mihirus/sm-thesis/cad/leakage-transformer-assembly/shunt-heat-sink.SLDPRT

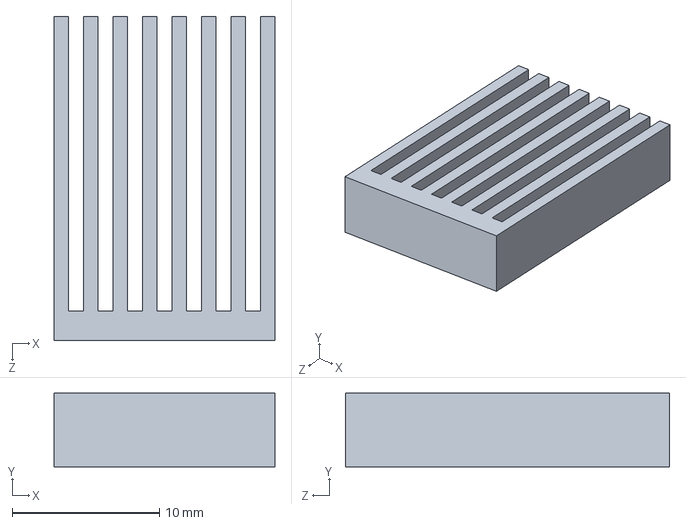
[picture p15: CAD file, 2025-12-01]
cad/leakage-transformer-assembly/shunt-heat-sink.SLDPRT
15.0 x 5.00 x 22.0 mm
