mihirus/sm-thesis/pcb/custom_assets/RM-0505S_P.step

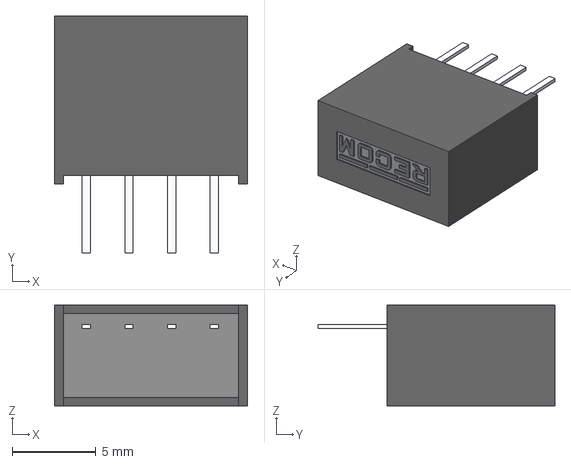
[picture p16: CAD file, 2025-12-01]
pcb/custom_assets/RM-0505S_P.step
11.5 x 14.1 x 6.00 mm
