mihirus/sm-thesis/cad/cores/etd59_core.SLDPRT

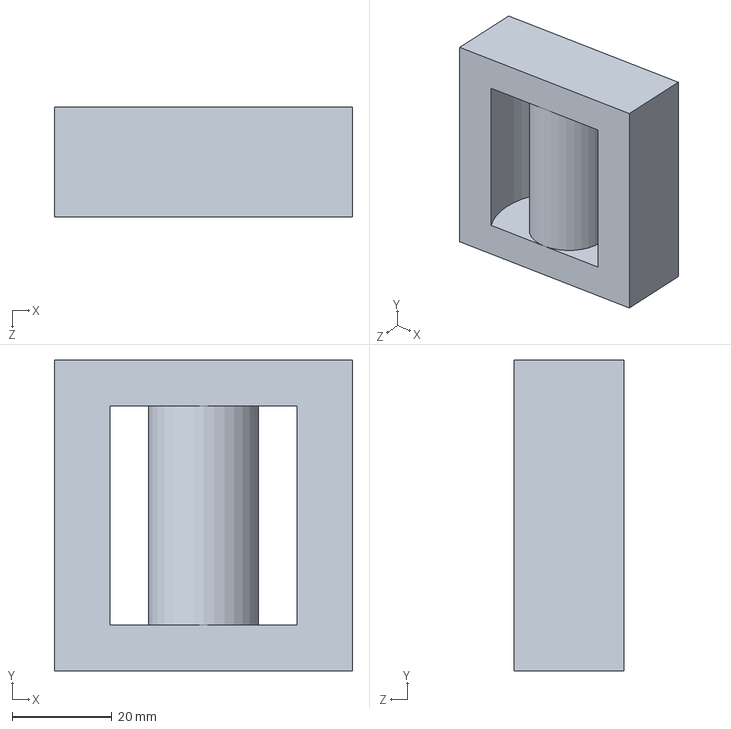
[picture p17: CAD file, 2025-12-01]
cad/cores/etd59_core.SLDPRT
59.8 x 62.4 x 22.1 mm
