mihirus/sm-thesis/cad/leakage-transformer-assembly/ETD59-integrated-base-raised-nov21.SLDPRT

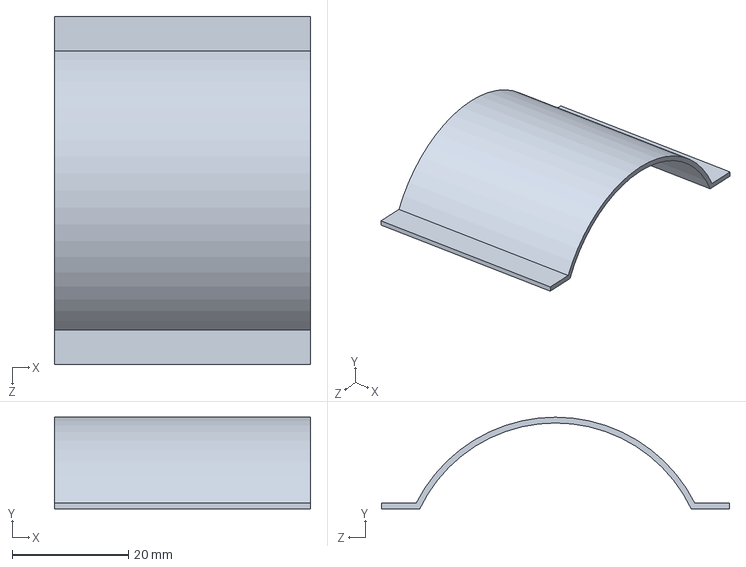
[picture p18: CAD file, 2025-12-01]
cad/leakage-transformer-assembly/ETD59-integrated-base-raised-nov21.SLDPRT
44.0 x 15.8 x 59.8 mm
