mihirus/sm-thesis/cad/leakage-transformer-assembly/ETD59-integrated-top-raised-0.8mm-dec9.SLDPRT

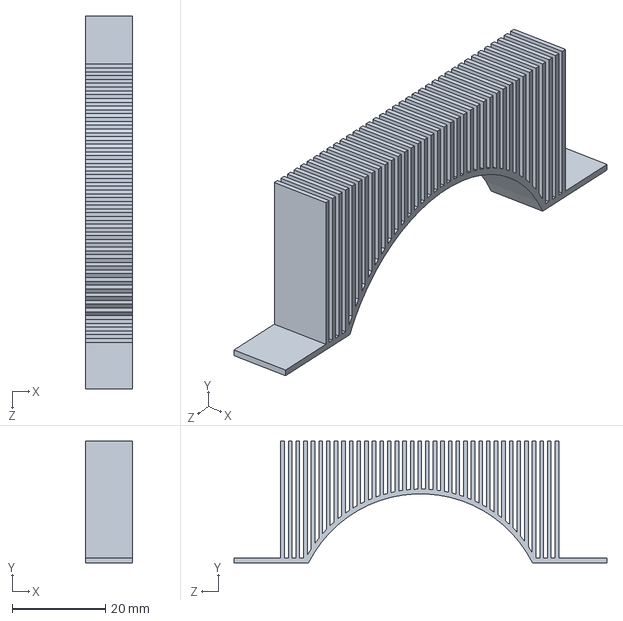
[picture p19: CAD file, 2025-12-01]
cad/leakage-transformer-assembly/ETD59-integrated-top-raised-0.8mm-dec9.SLDPRT
10.0 x 26.0 x 79.8 mm
