mihirus/sm-thesis/cad/leakage-transformer-assembly/etd59_bobbin_integrated_v7.SLDPRT

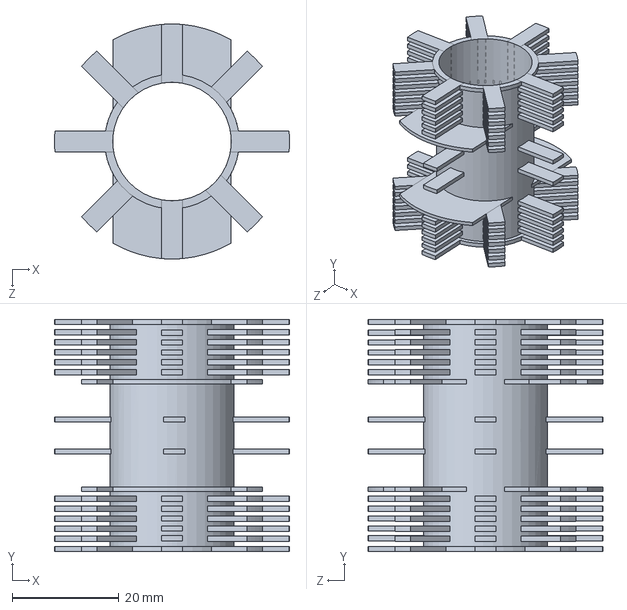
[picture p20: CAD file, 2025-12-01]
cad/leakage-transformer-assembly/etd59_bobbin_integrated_v7.SLDPRT
44.0 x 43.5 x 44.0 mm
