mihirus/sm-thesis/cad/leakage-transformer-assembly/ETD59-integrated-bottom-raised-0.8mm-dec9.SLDPRT

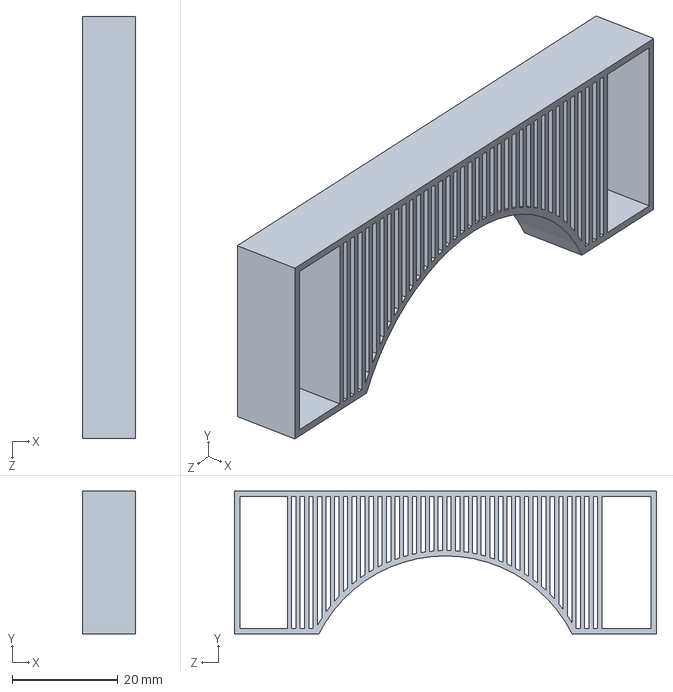
[picture p21: CAD file, 2025-12-01]
cad/leakage-transformer-assembly/ETD59-integrated-bottom-raised-0.8mm-dec9.SLDPRT
10.0 x 27.0 x 79.8 mm
